Zahra-Navabi/CV_Craniobot_published/CAD_files/OCT camera.SLDPRT

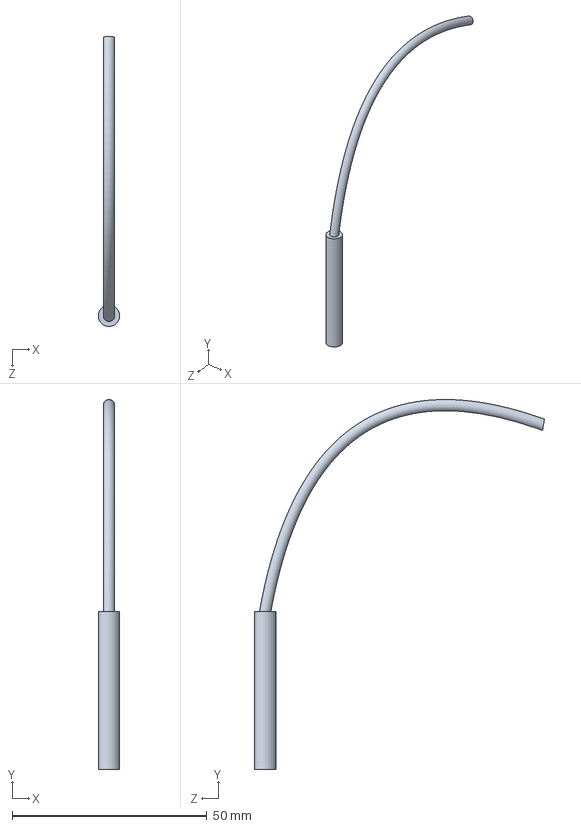
[picture p15: CAD file, 2024-12-11]
CAD_files/OCT camera.SLDPRT
5.50 x 95.1 x 74.5 mm
