Zahra-Navabi/CV_Craniobot_published/CAD_files/XE75A90-Solidworks.sldprt

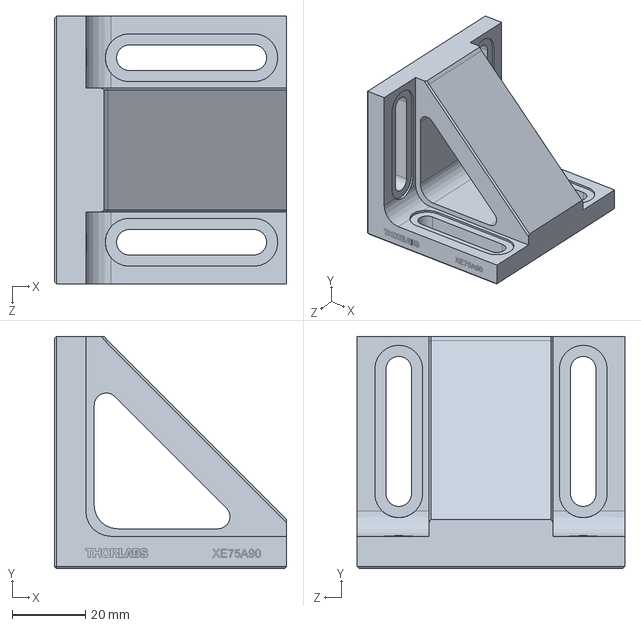
[picture p16: CAD file, 2024-12-11]
CAD_files/XE75A90-Solidworks.sldprt
63.5 x 63.5 x 73.2 mm
