Zahra-Navabi/CV_Craniobot_published/CAD_files/A-00001 - STD SCANNER.STEP

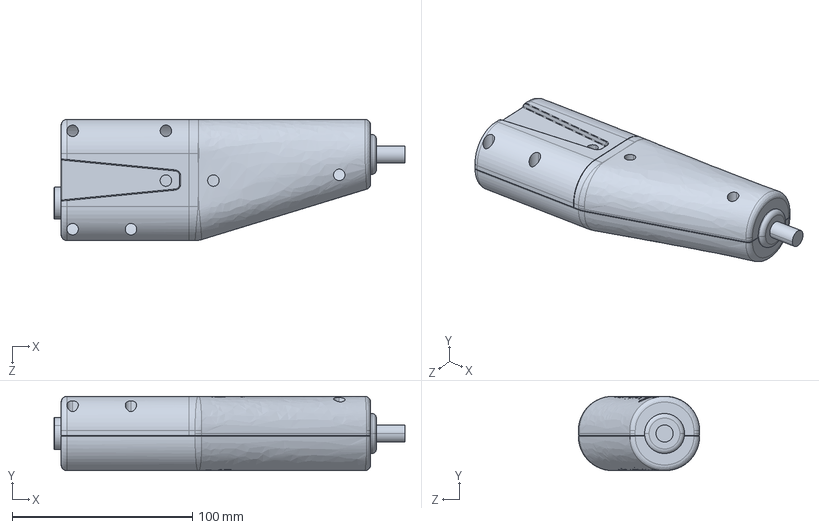
[picture p17: CAD file, 2024-12-11]
CAD_files/A-00001 - STD SCANNER.STEP
194.8 x 41.3 x 67.3 mm
