Zahra-Navabi/CV_Craniobot_published/CAD_files/XE5075L20-Solidworks.sldprt

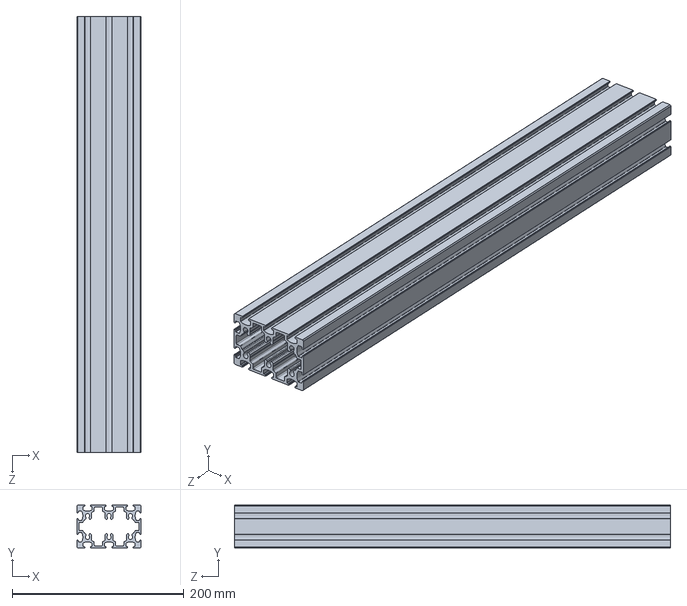
[picture p18: CAD file, 2024-12-11]
CAD_files/XE5075L20-Solidworks.sldprt
75.0 x 50.0 x 508.0 mm
