Zahra-Navabi/CV_Craniobot_published/CAD_files/MTS25_M-Z8-Solidworks.sldprt

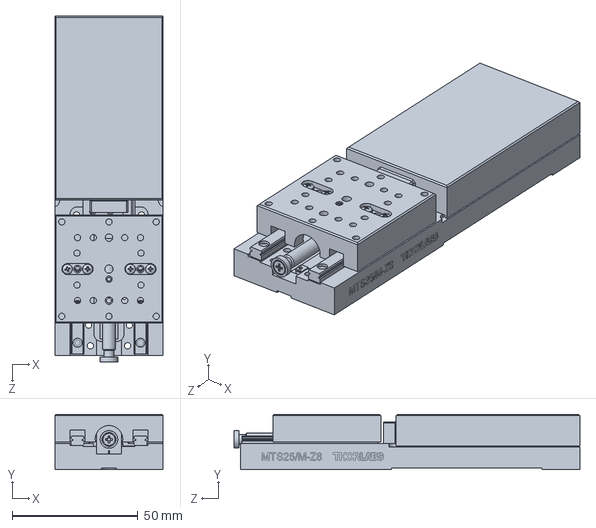
[picture p19: CAD file, 2024-12-11]
CAD_files/MTS25_M-Z8-Solidworks.sldprt
43.0 x 22.0 x 137.4 mm
