Zahra-Navabi/CV_Craniobot_published/CAD_files/MB4A-Solidworks.sldprt

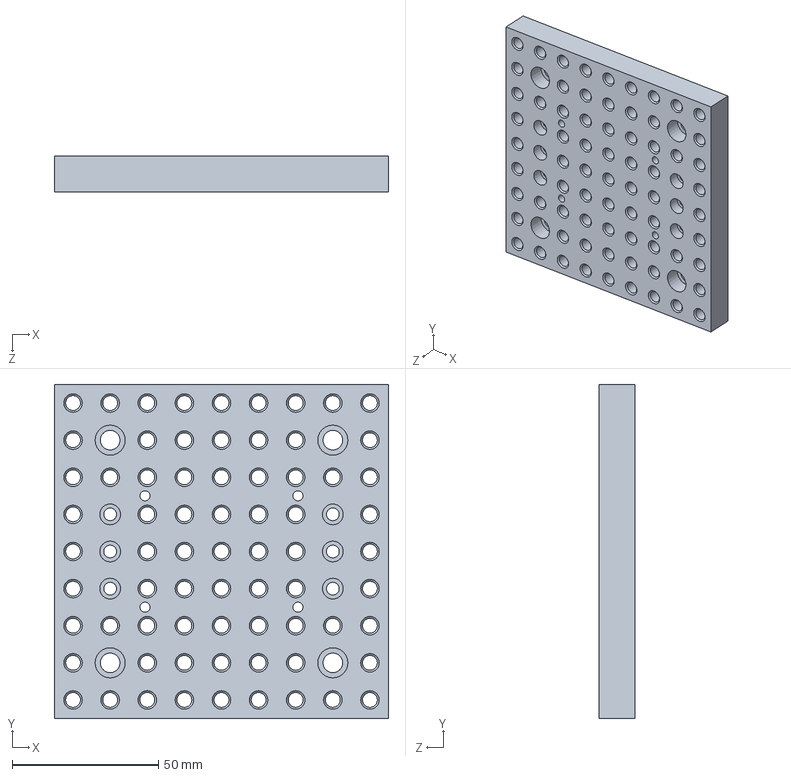
[picture p20: CAD file, 2024-12-11]
CAD_files/MB4A-Solidworks.sldprt
114.3 x 114.3 x 12.2 mm
